freder202/weather_pill/WeatherPill/imported/USBLC6_2P6/USBLC6-2P6.step

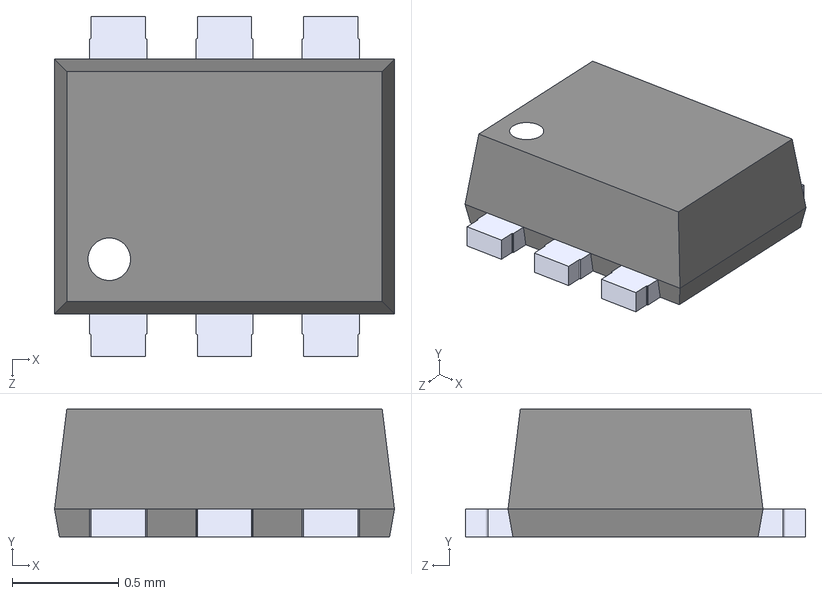
[picture p20: CAD file, 2025-08-07]
WeatherPill/imported/USBLC6_2P6/USBLC6-2P6.step
1.60 x 0.6 x 1.60 mm
