freder202/weather_pill/WeatherPill/imported/TPS22916CYFPR/TPS22916CYFPR.step

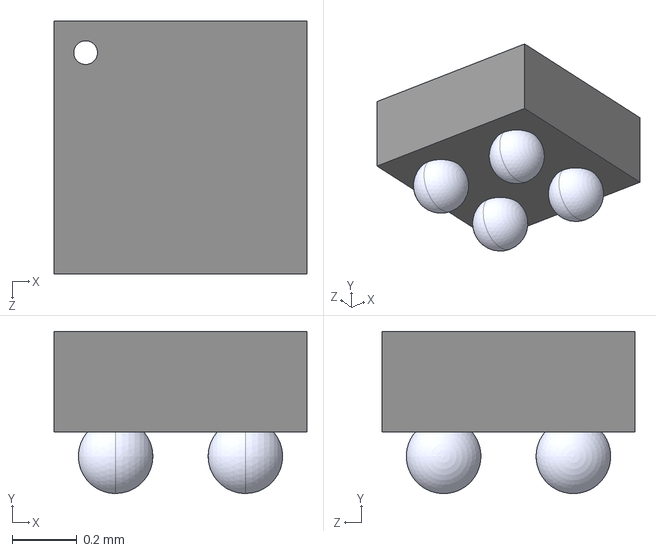
[picture p21: CAD file, 2025-08-07]
WeatherPill/imported/TPS22916CYFPR/TPS22916CYFPR.step
0.78 x 0.5 x 0.78 mm
