freder202/weather_pill/WeatherPill/imported/USB12402012E212A/12402012E212A--3DModel-STEP-533217.STEP

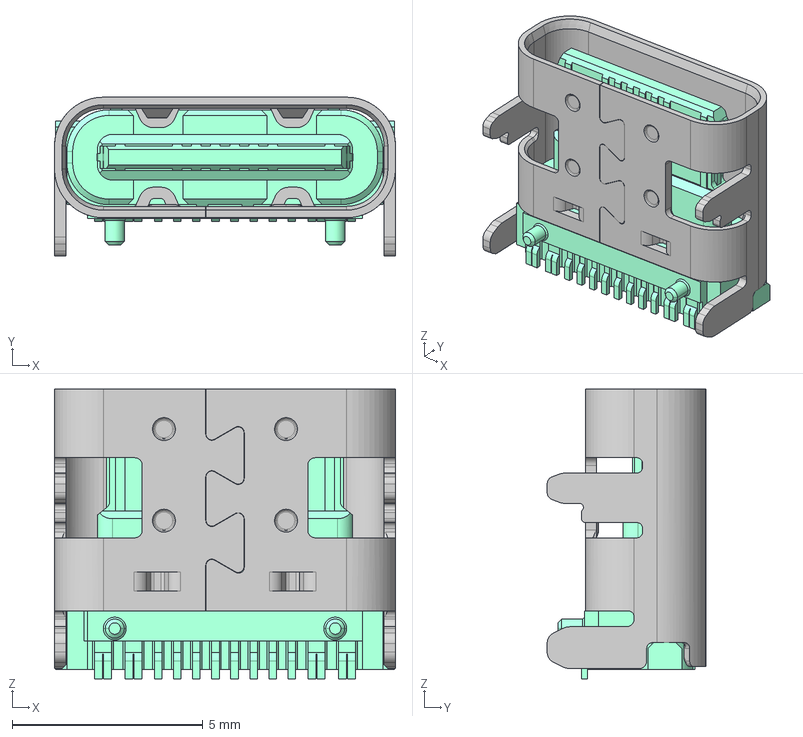
[picture p22: CAD file, 2023-06-12]
WeatherPill/imported/USB12402012E212A/12402012E212A--3DModel-STEP-533217.STEP
8.94 x 4.16 x 7.60 mm
